TomasWityk/Proyecto-Mecatronica/Registros audiovisuales Segway Monkey/Arduino.jpg

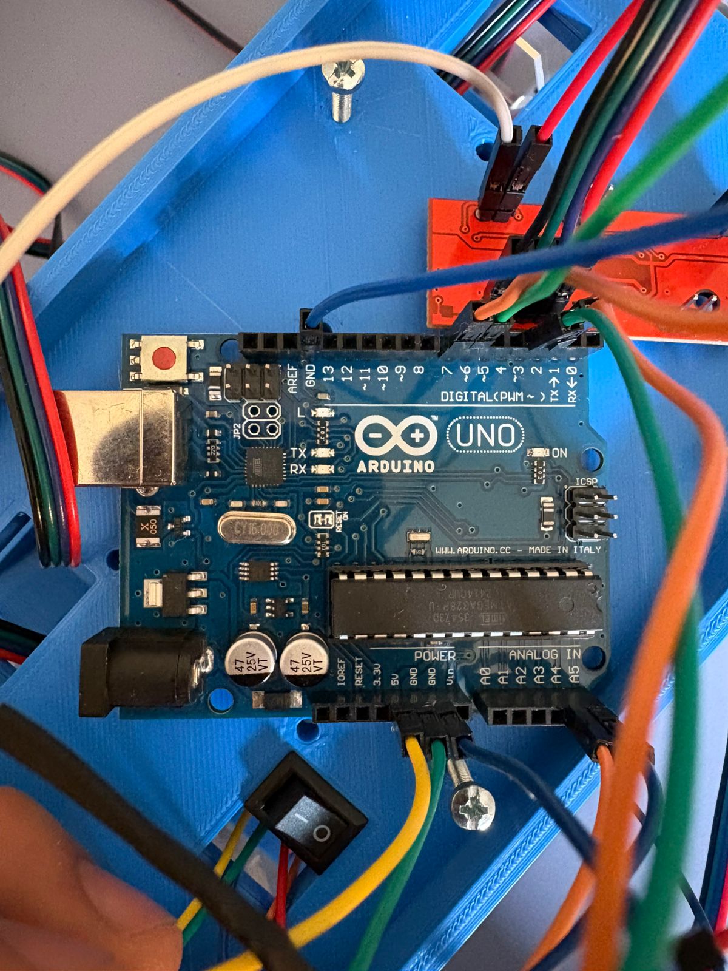
Registros audiovisuales Segway Monkey/Arduino.jpg
