TomasWityk/Proyecto-Mecatronica/Registros audiovisuales Segway Monkey/Easydriver.jpg

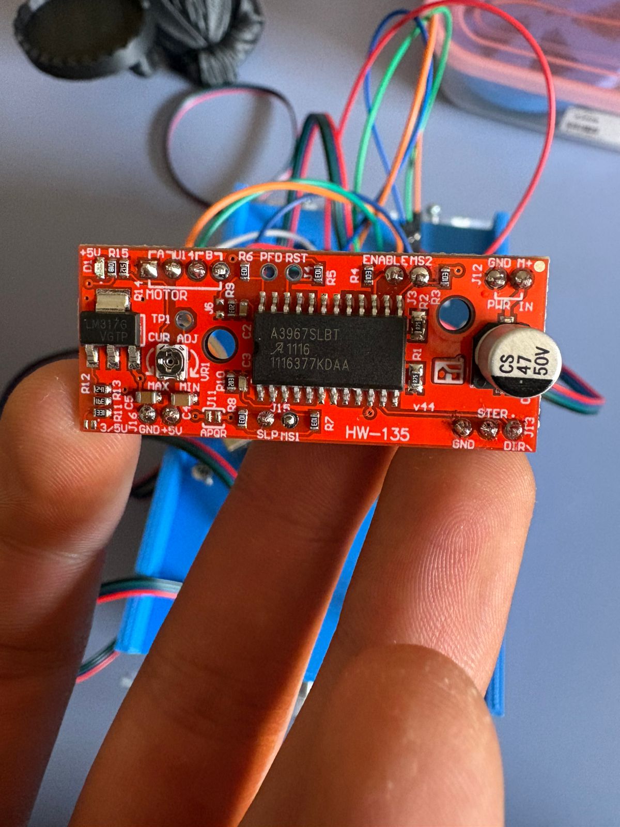
Registros audiovisuales Segway Monkey/Easydriver.jpg
